odonnellf/CSAW/design/Architecture Diagram/CSAW_ArchDiagram.jpg

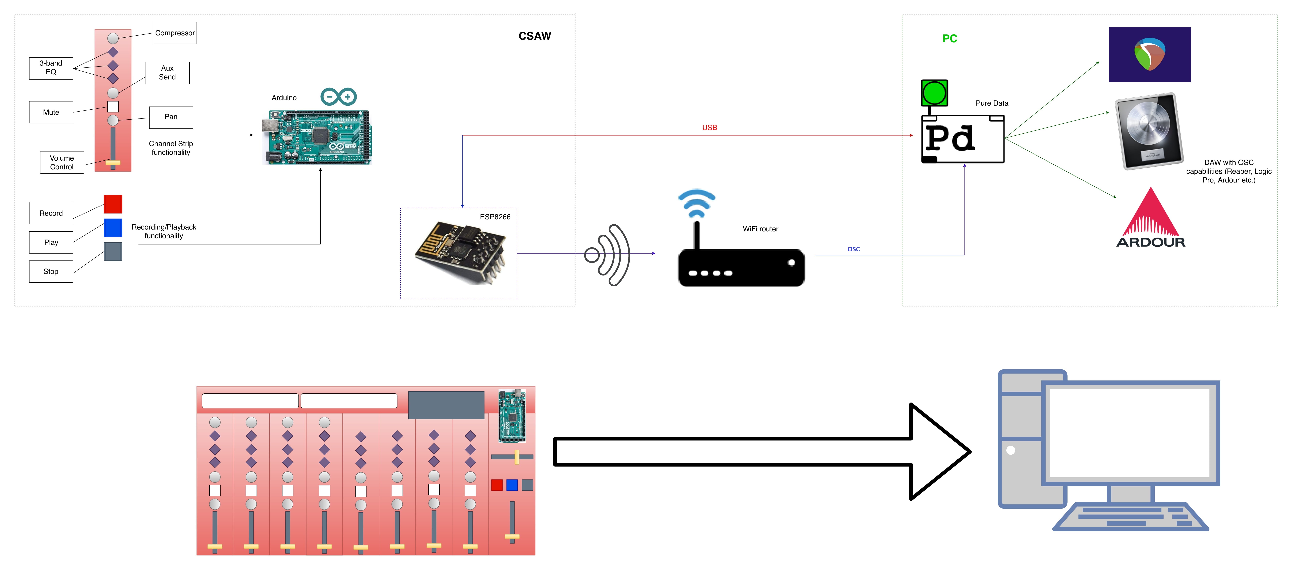
design/Architecture Diagram/CSAW_ArchDiagram.jpg
