odonnellf/CSAW/design/Arduino Diagram/KeyLegend.PNG

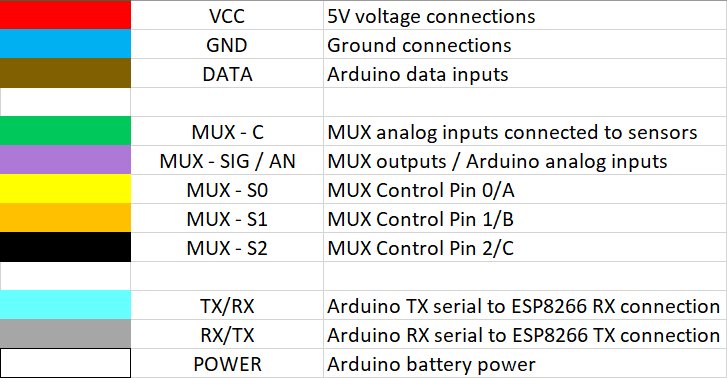
design/Arduino Diagram/KeyLegend.PNG
