odonnellf/CSAW/design/Arduino Schematic/CSAWSchematic2.png

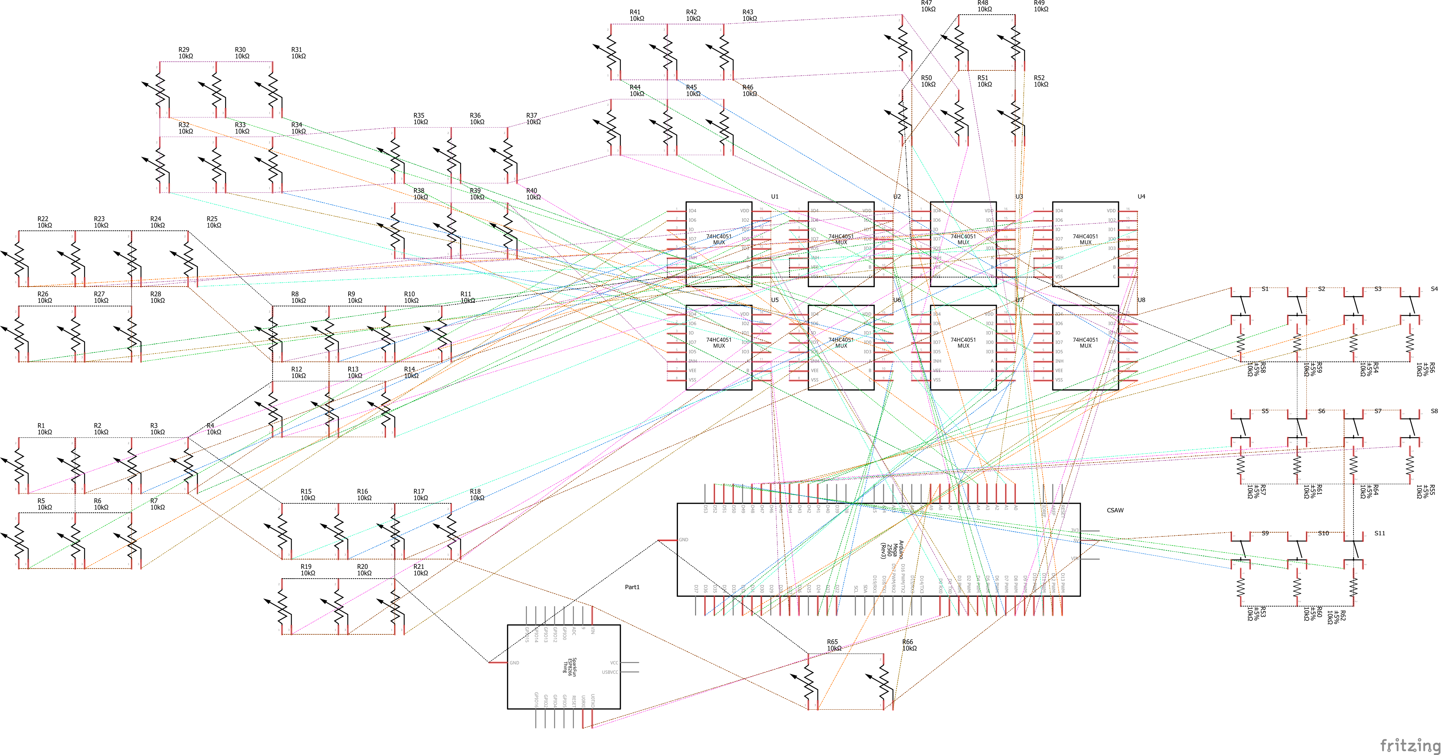
design/Arduino Schematic/CSAWSchematic2.png
