odonnellf/CSAW/design/Gantt Charts/0. CSAW_GanttOverview.png

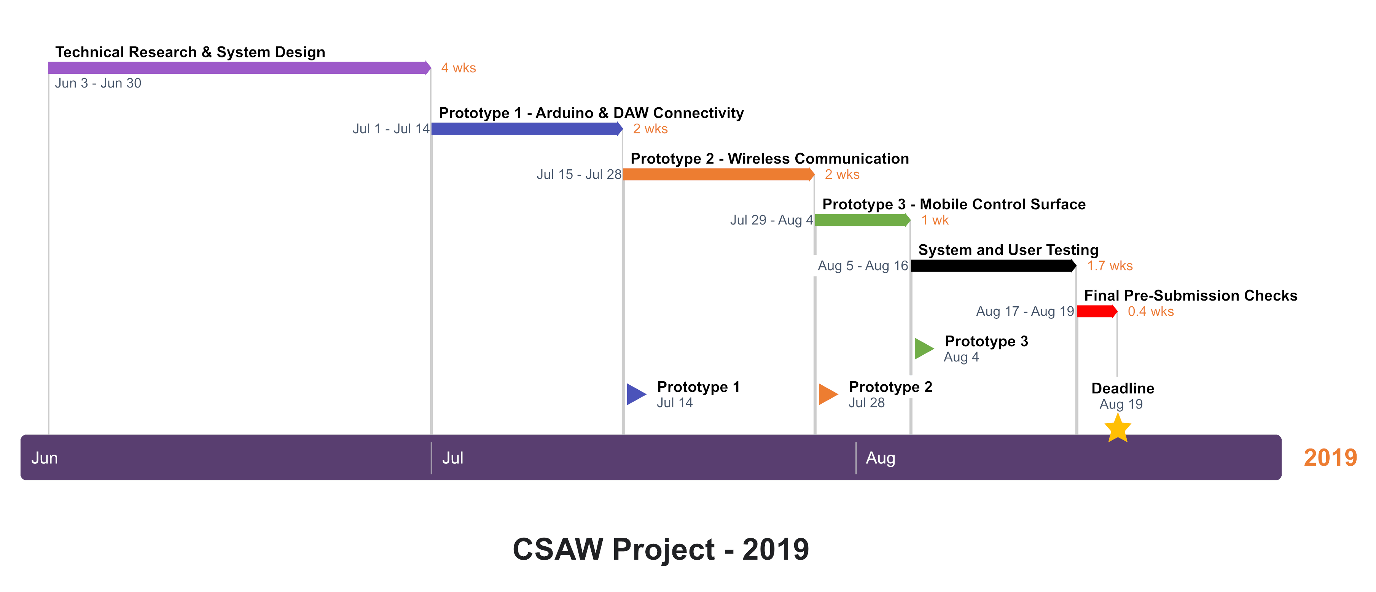
design/Gantt Charts/0. CSAW_GanttOverview.png
