odonnellf/CSAW/design/Gantt Charts/1. Technical Research & System Design.png

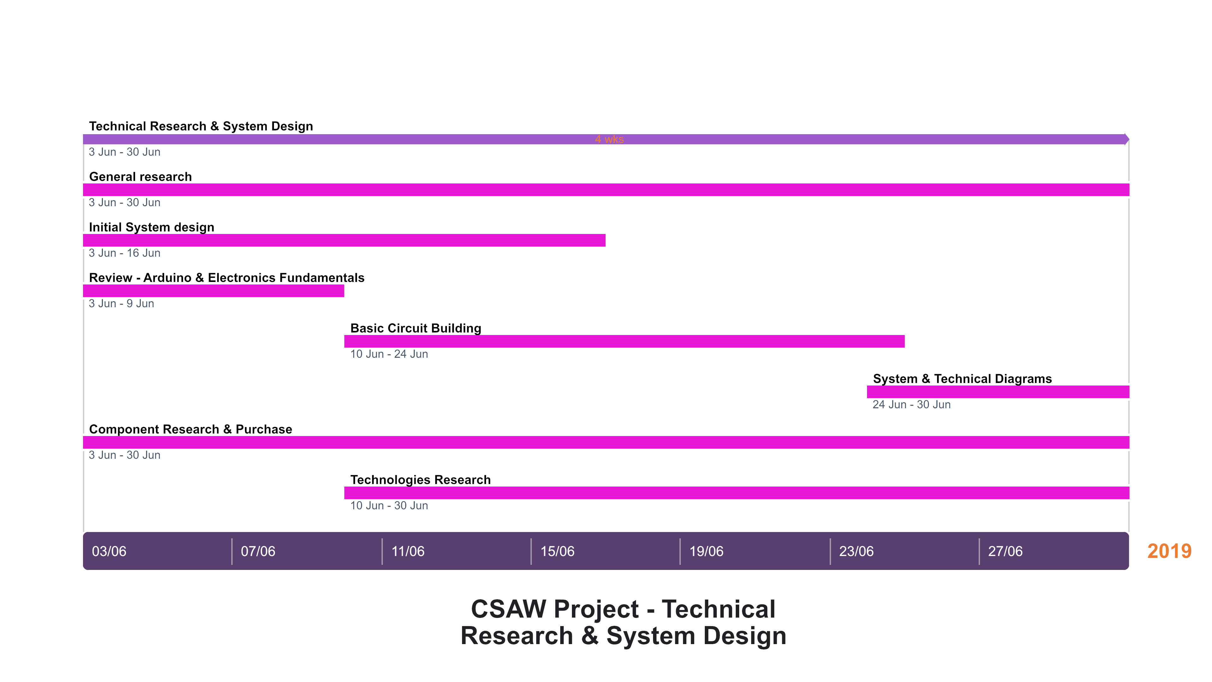
design/Gantt Charts/1. Technical Research & System Design.png
