odonnellf/CSAW/design/Gantt Charts/2. Prototype 1 - Arduino & DAW Connectivity.png

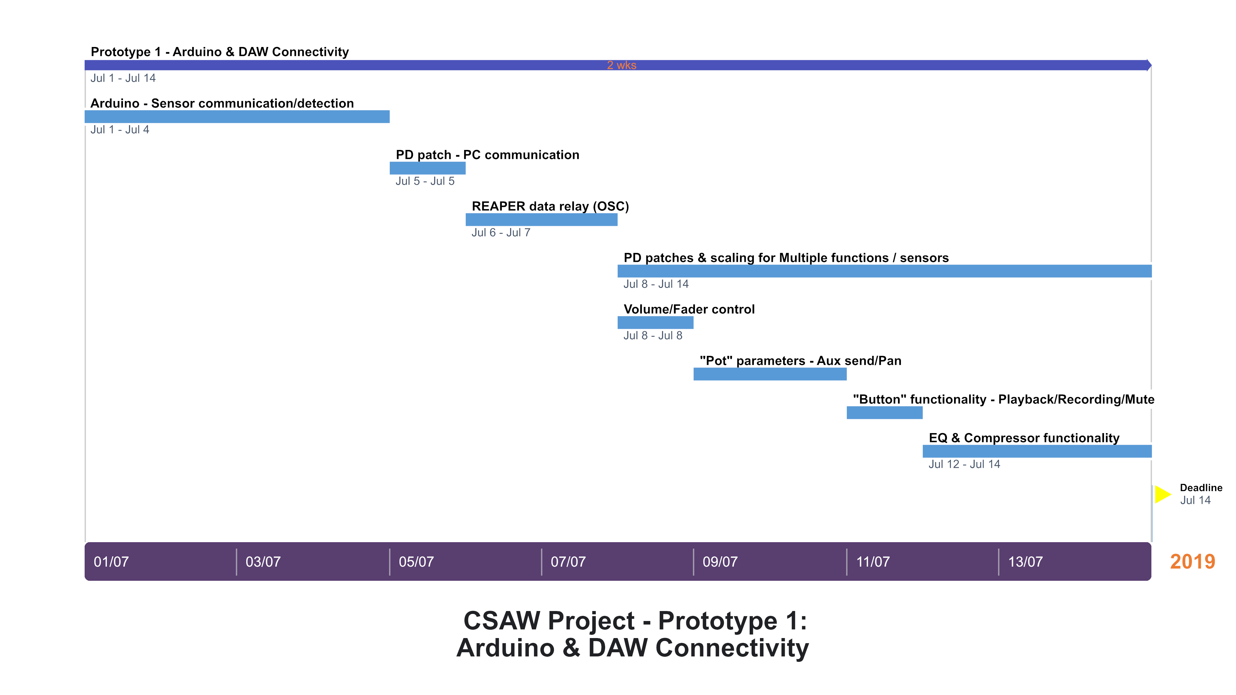
design/Gantt Charts/2. Prototype 1 - Arduino & DAW Connectivity.png
