odonnellf/CSAW/design/Gantt Charts/3. Prototype 2 - Wireless Communication.png

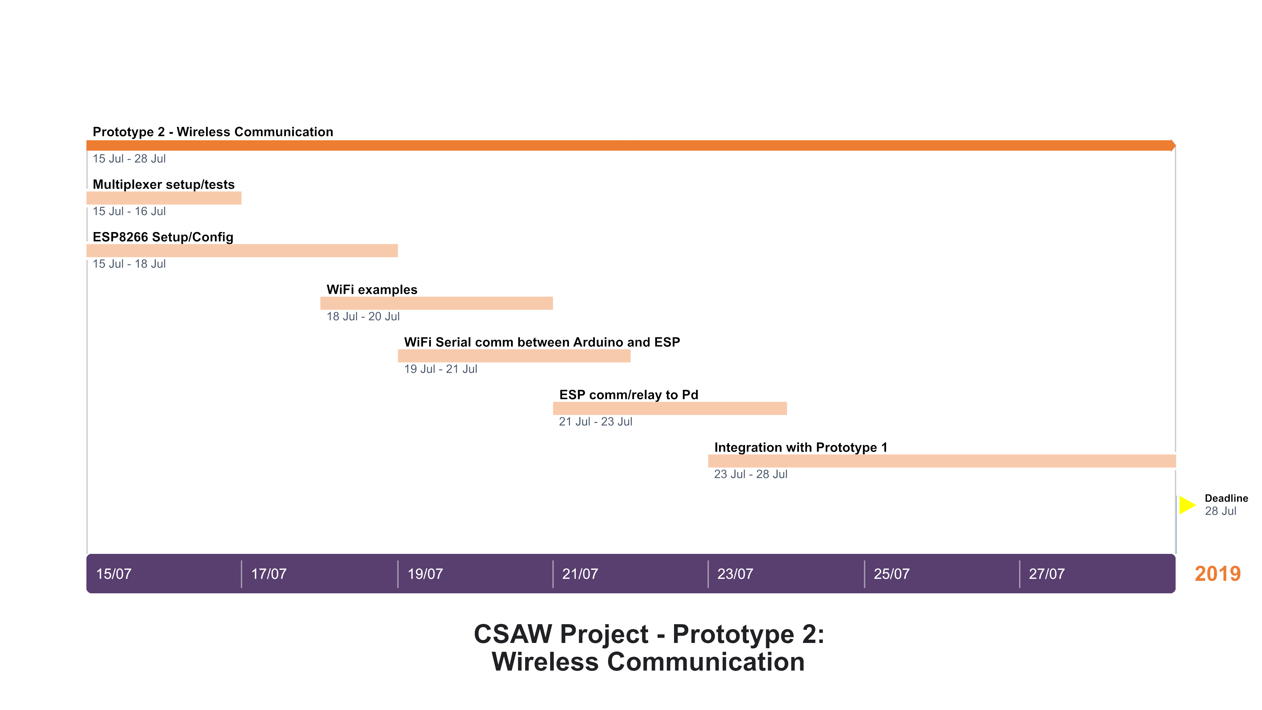
design/Gantt Charts/3. Prototype 2 - Wireless Communication.png
