odonnellf/CSAW/design/Gantt Charts/4. Prototype 3 - Mobile Control Surface.png

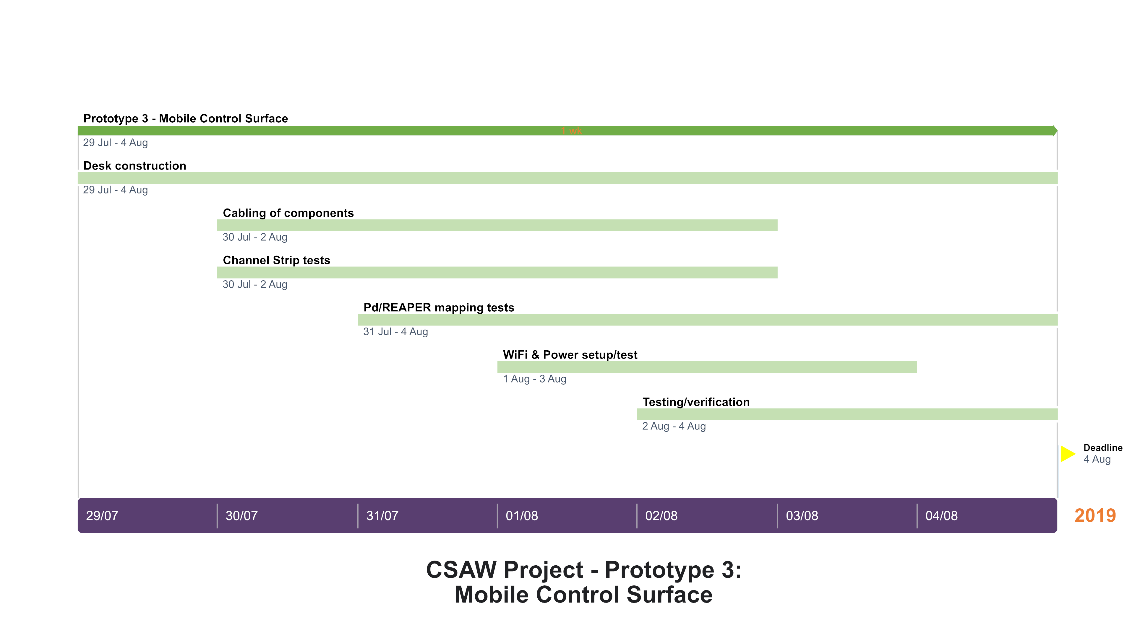
design/Gantt Charts/4. Prototype 3 - Mobile Control Surface.png
