odonnellf/CSAW/design/SDLC/Waterfall.png

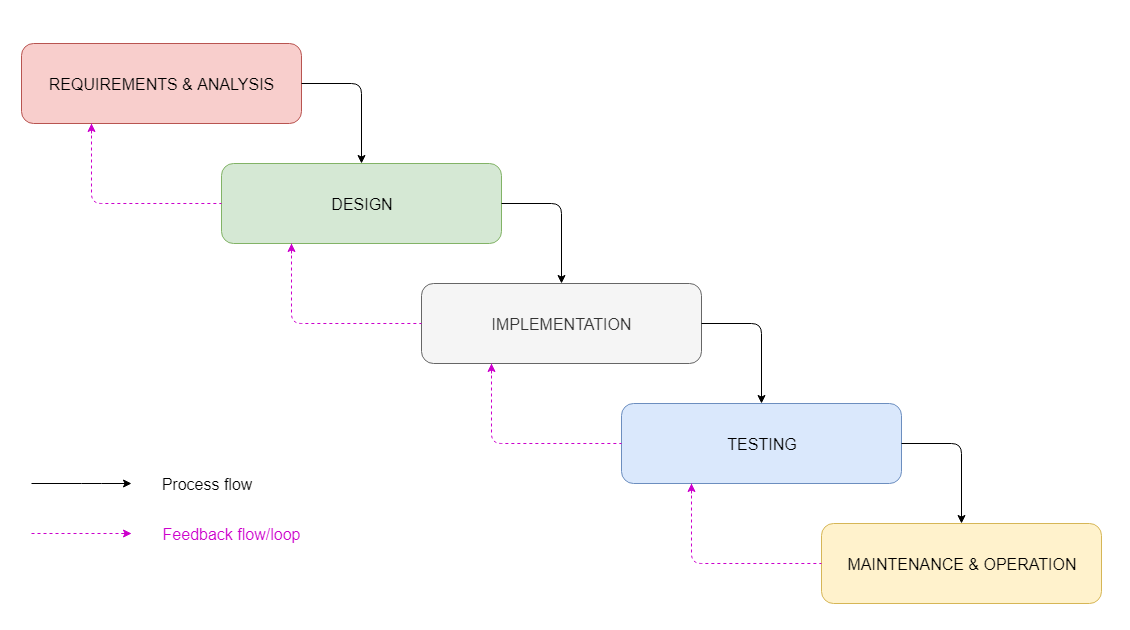
design/SDLC/Waterfall.png
