odonnellf/CSAW/design/Materials/Materials.png

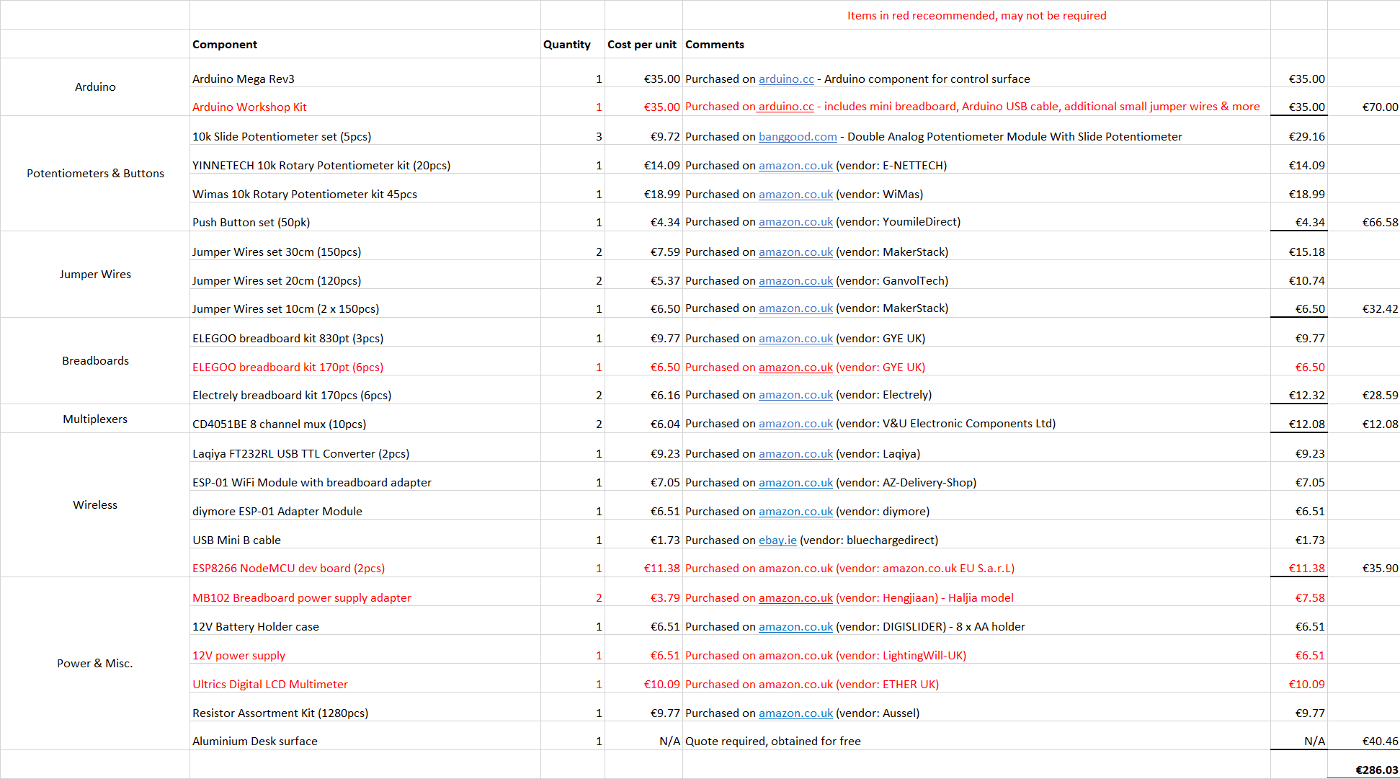
design/Materials/Materials.png
