odonnellf/CSAW/design/Gantt Charts/5. System & User Testing.png

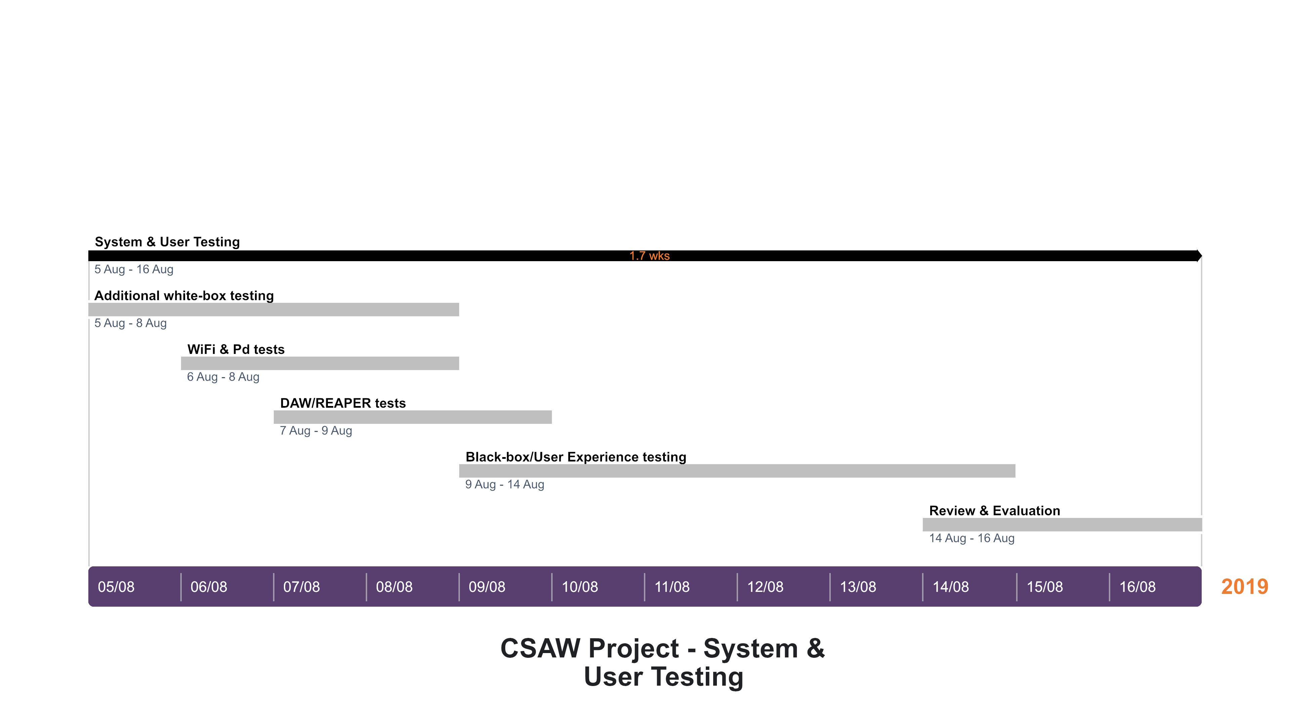
design/Gantt Charts/5. System & User Testing.png
