odonnellf/CSAW/design/Measurements/Measurements.png

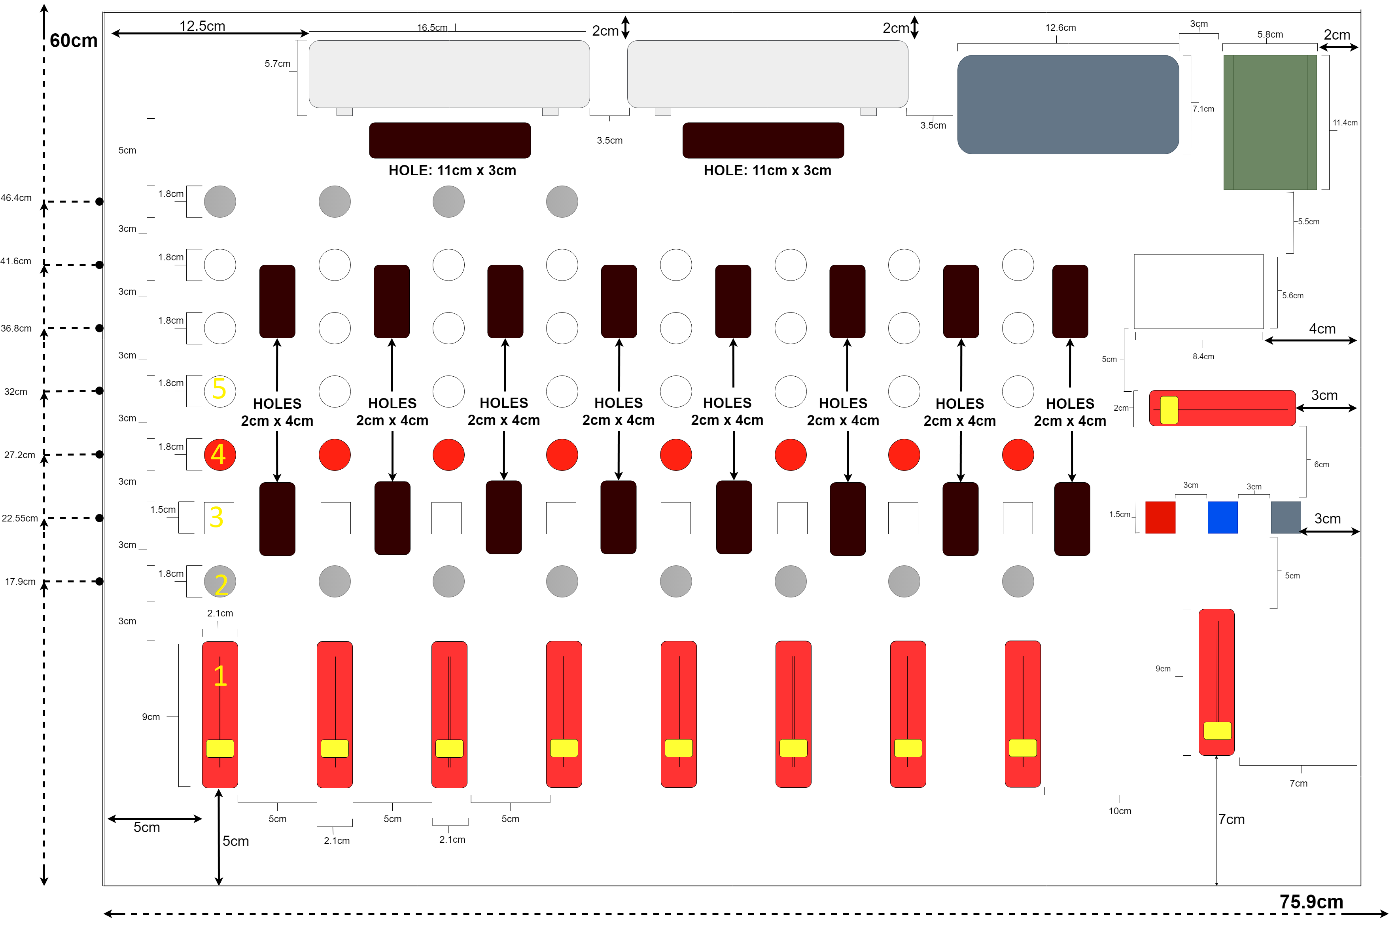
design/Measurements/Measurements.png
